JonathanFerron/Citrouille90/doc/20260207_201149.jpg

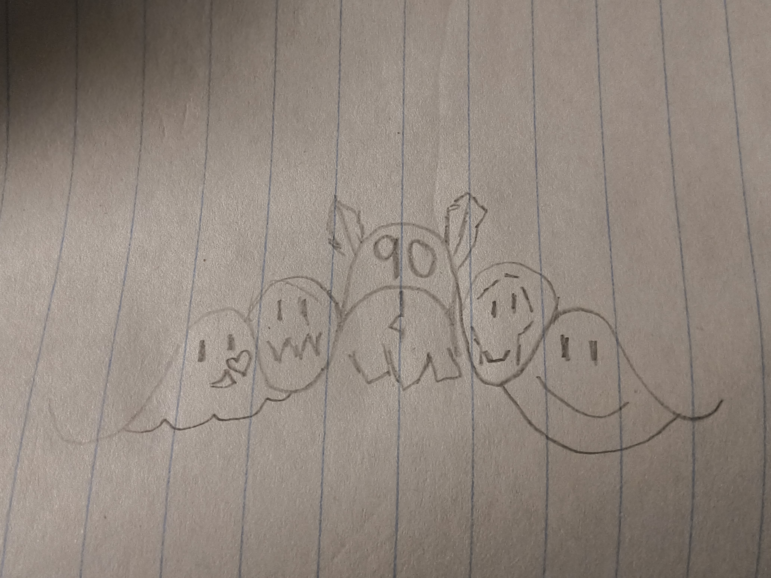
doc/20260207_201149.jpg
