JonathanFerron/Citrouille90/doc/20260313_123038.jpg

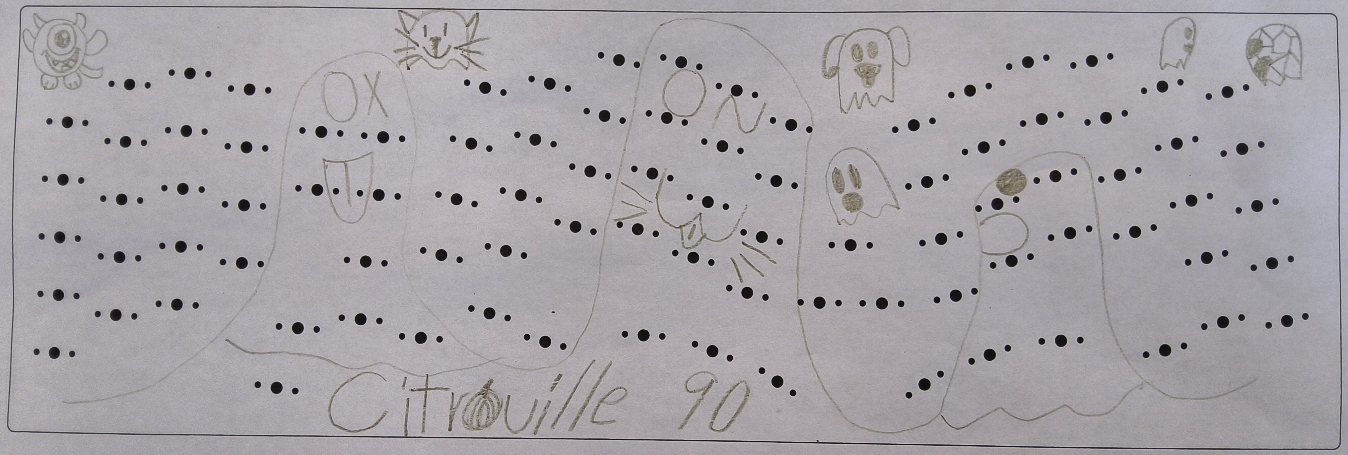
doc/20260313_123038.jpg
