JonathanFerron/Citrouille90/doc/Citrouille90_stackup_layered.tiff

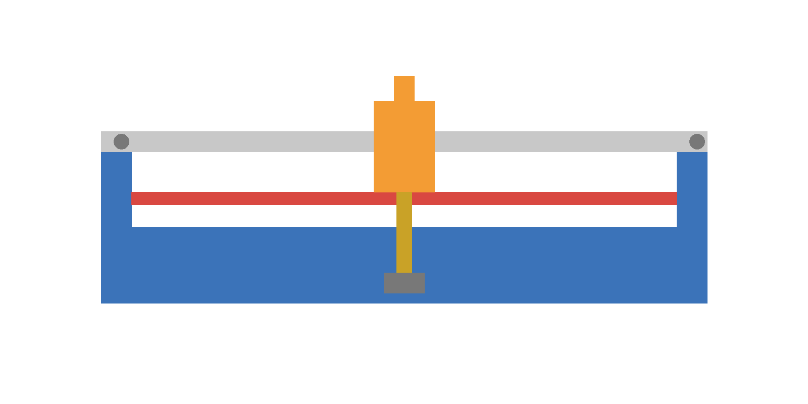
doc/Citrouille90_stackup_layered.tiff
