JonathanFerron/Citrouille90/doc/file_00000000d7c871f59067af61fc4f17ec (1).png

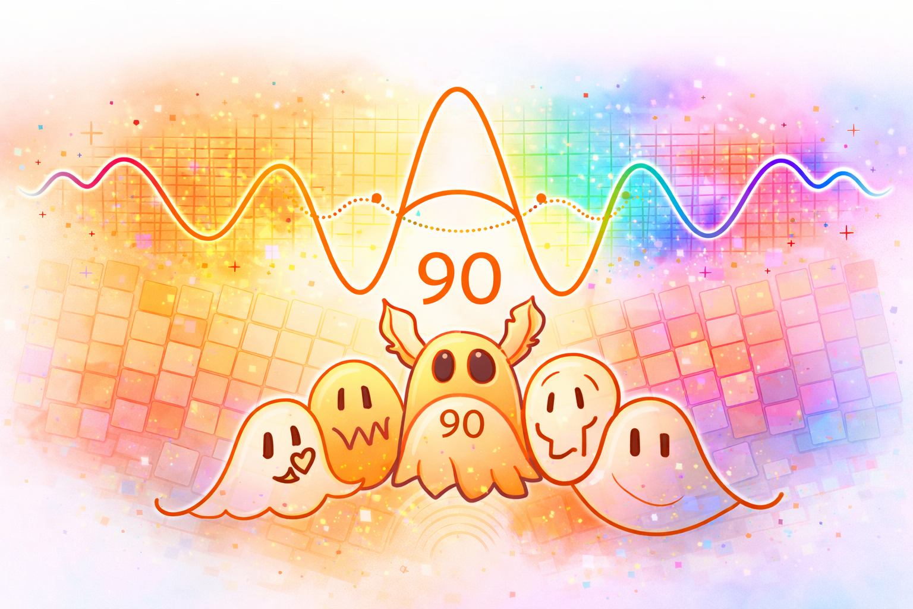
doc/file_00000000d7c871f59067af61fc4f17ec (1).png
