JonathanFerron/Citrouille90/doc/file_00000000f6e471f7b5d3dcd0db7e743c.png

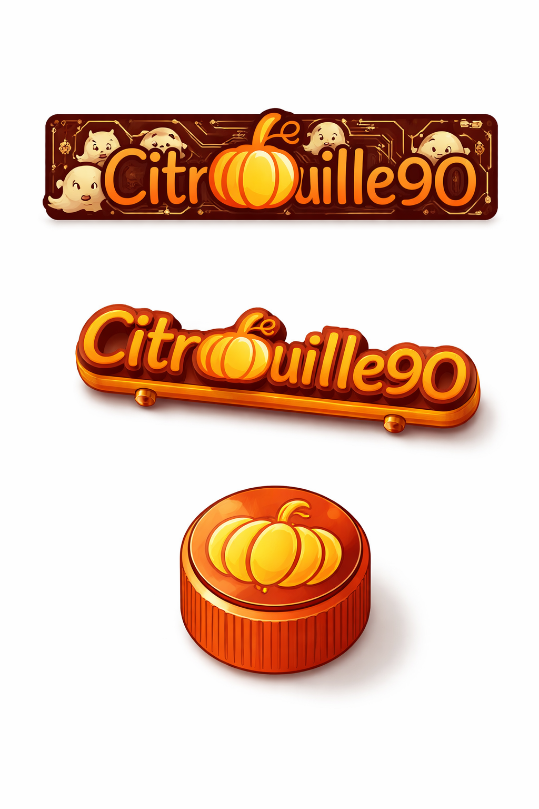
doc/file_00000000f6e471f7b5d3dcd0db7e743c.png
