JonathanFerron/Citrouille90/doc/file_000000008a08720c9a9e2993dab95d04.png

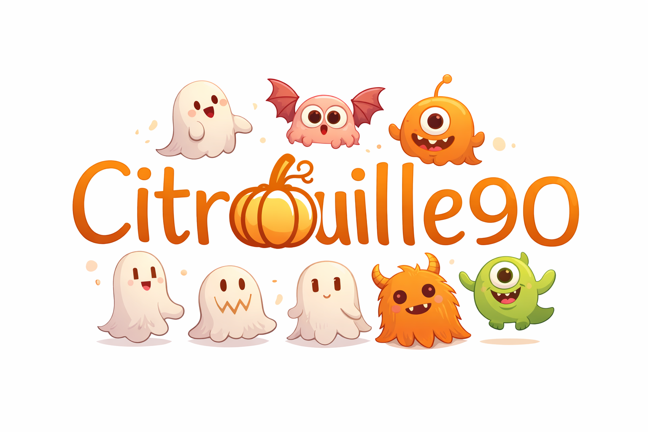
doc/file_000000008a08720c9a9e2993dab95d04.png
