JonathanFerron/Citrouille90/doc/file_0000000008ac71f7b7ef34ee5ffa98f1.png

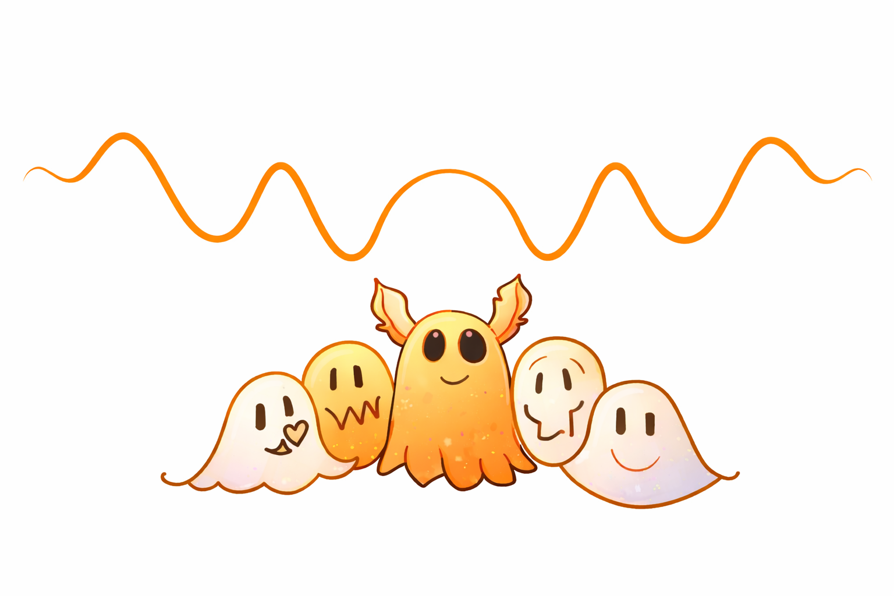
doc/file_0000000008ac71f7b7ef34ee5ffa98f1.png
