JonathanFerron/Citrouille90/doc/file_000000008d7071f783d772ec0bde2197.png

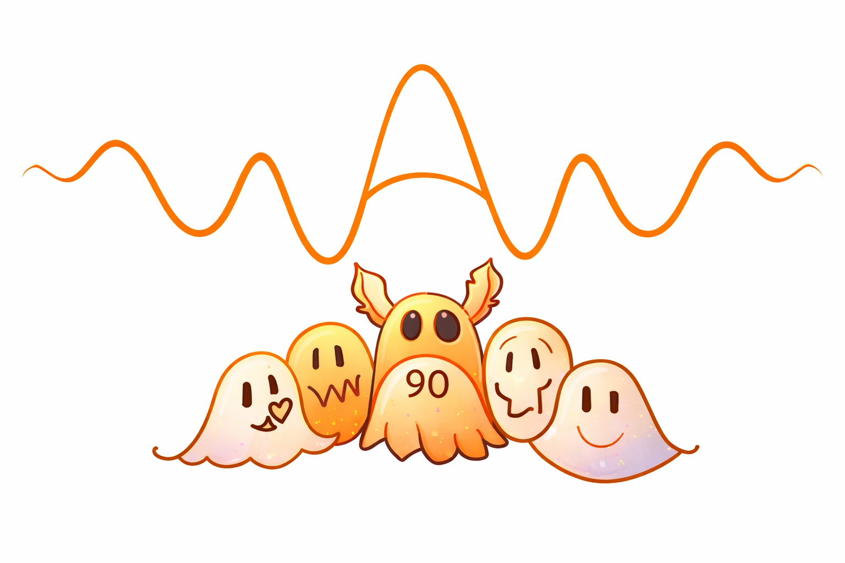
doc/file_000000008d7071f783d772ec0bde2197.png
