JonathanFerron/Citrouille90/doc/file_0000000013c871fd81ed29485cb378ce.png

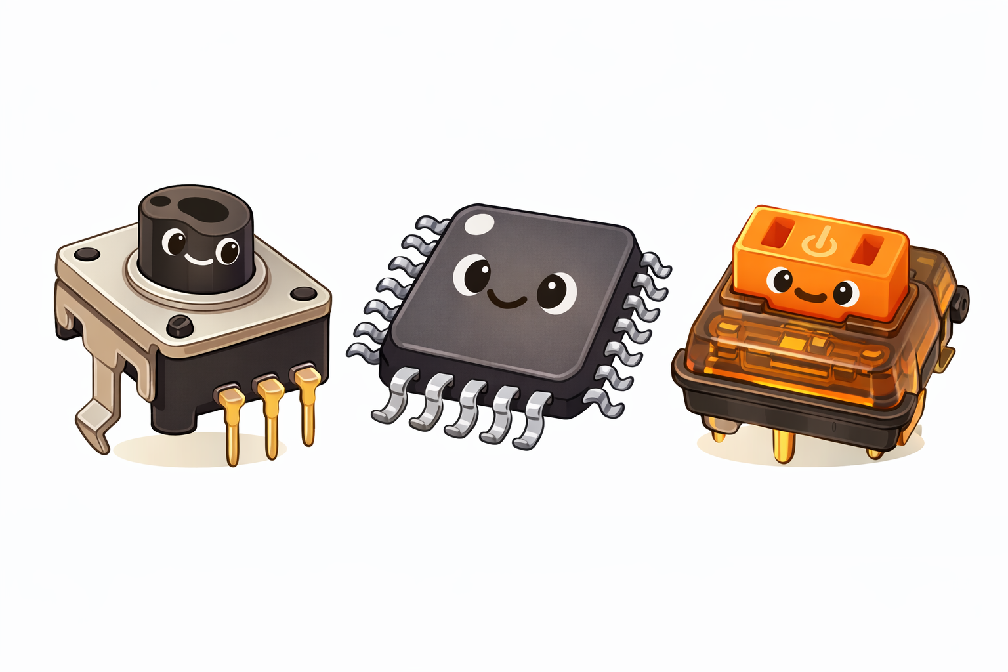
doc/file_0000000013c871fd81ed29485cb378ce.png
