JonathanFerron/Citrouille90/doc/file_00000000723c71fd9b8faab6fcd9ef8c.png

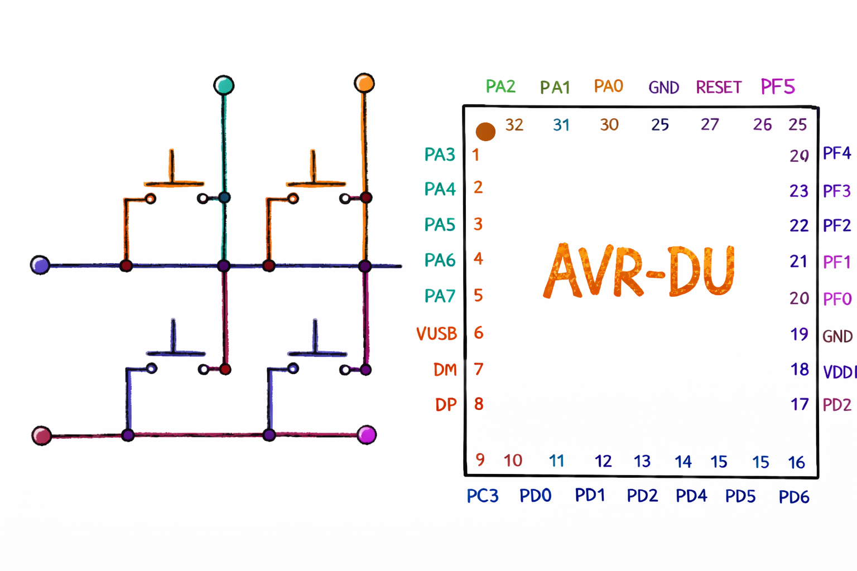
doc/file_00000000723c71fd9b8faab6fcd9ef8c.png
