JonathanFerron/Citrouille90/doc/file_00000000823c71f583ad2a410682e7db (1).png

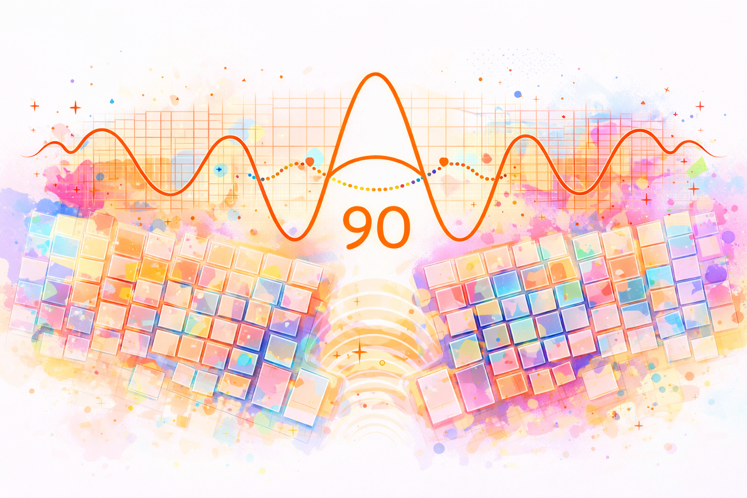
doc/file_00000000823c71f583ad2a410682e7db (1).png
