JonathanFerron/Citrouille90/doc/file_000000002094722fa4f8a808bf9c1e9a.png

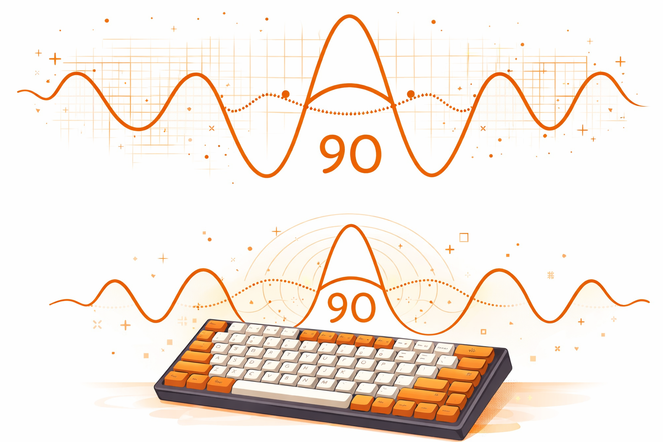
doc/file_000000002094722fa4f8a808bf9c1e9a.png
