JonathanFerron/Citrouille90/doc/Friendly ghost in motion.png

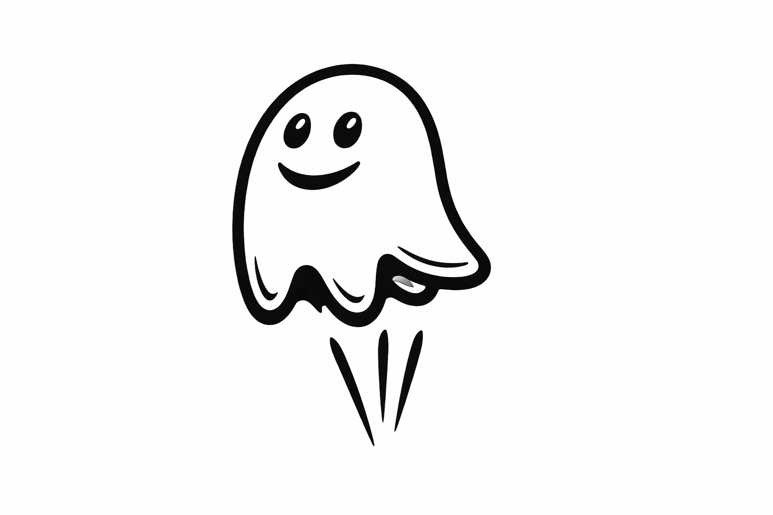
doc/Friendly ghost in motion.png
