JonathanFerron/Citrouille90/doc/Screenshot_20260206_212824_Drive.jpg

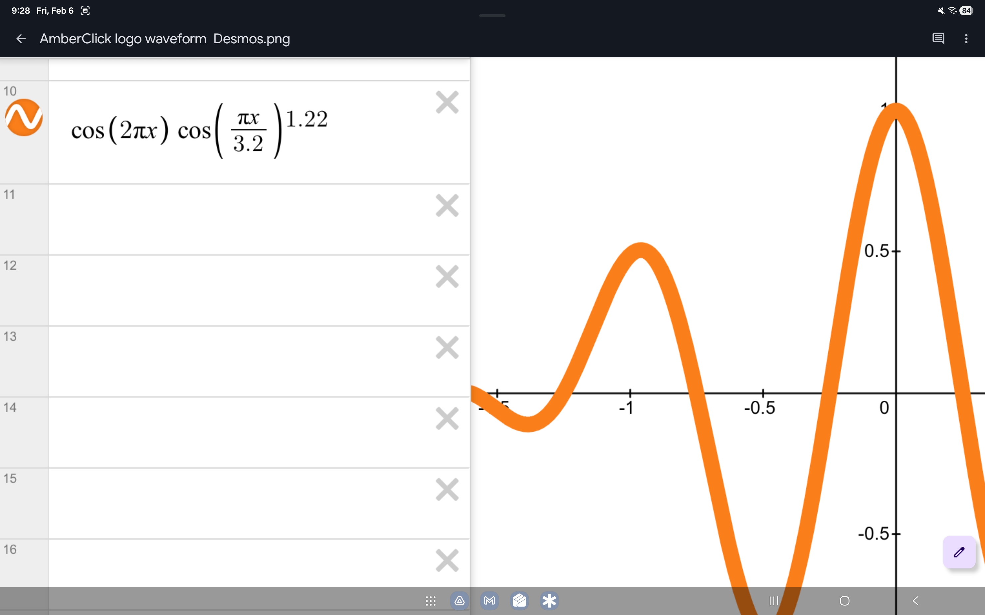
doc/Screenshot_20260206_212824_Drive.jpg
