JonathanFerron/Citrouille90/doc/Screenshot_20260207_200041_Drive.jpg

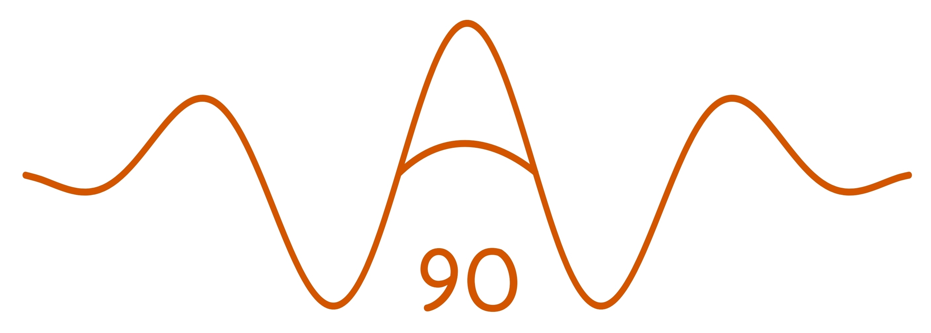
doc/Screenshot_20260207_200041_Drive.jpg
