JonathanFerron/Citrouille90/doc/Screenshot_20260213_221005_Chrome.jpg

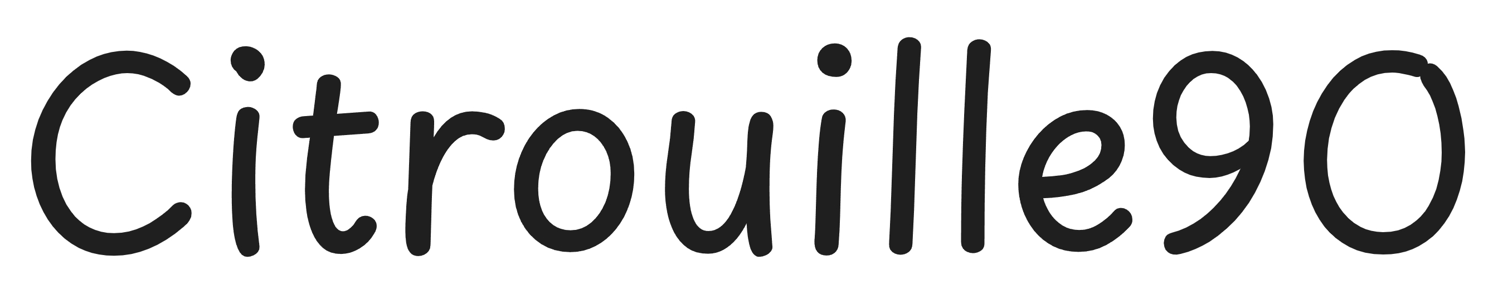
doc/Screenshot_20260213_221005_Chrome.jpg
