JonathanFerron/Citrouille90/doc/Screenshot_20260221_145438_Chrome.jpg

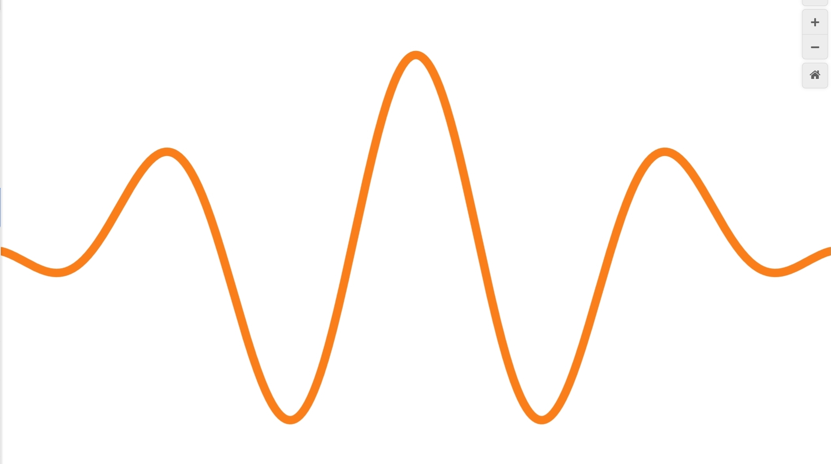
doc/Screenshot_20260221_145438_Chrome.jpg
