JonathanFerron/Citrouille90/encoderknob/Citrouille simple.jpg

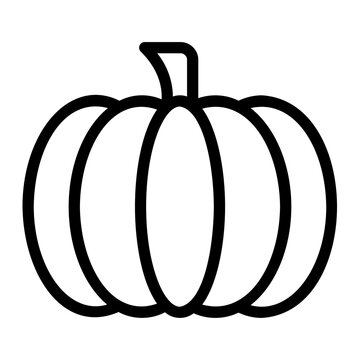
encoderknob/Citrouille simple.jpg
