JonathanFerron/Citrouille90/kbpcbold2/lib_3Dmodels/PES12-40S-N0024.stp

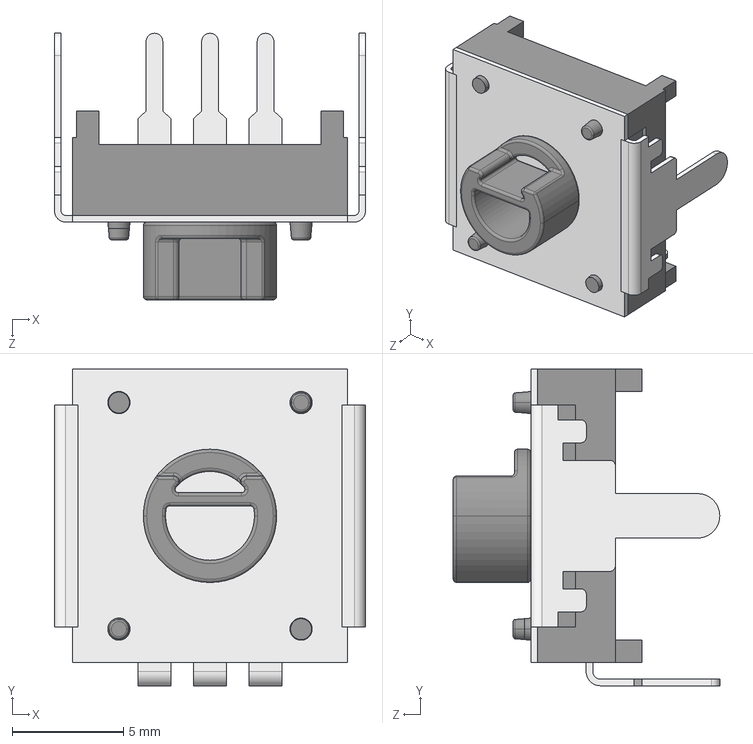
[picture p36: CAD file, 2026-03-11]
kbpcbold2/lib_3Dmodels/PES12-40S-N0024.stp
14.0 x 14.2 x 12.0 mm
